jasoneplumb/infobento.com/previews/A-commuter.png

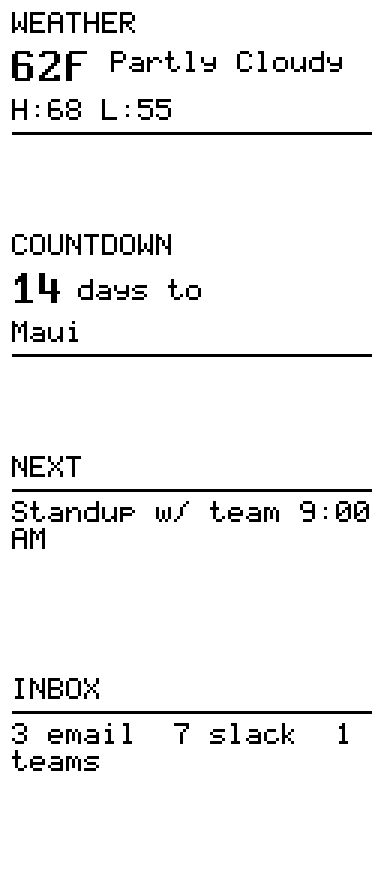
previews/A-commuter.png
