jasoneplumb/infobento.com/previews/C-networking-3color.png

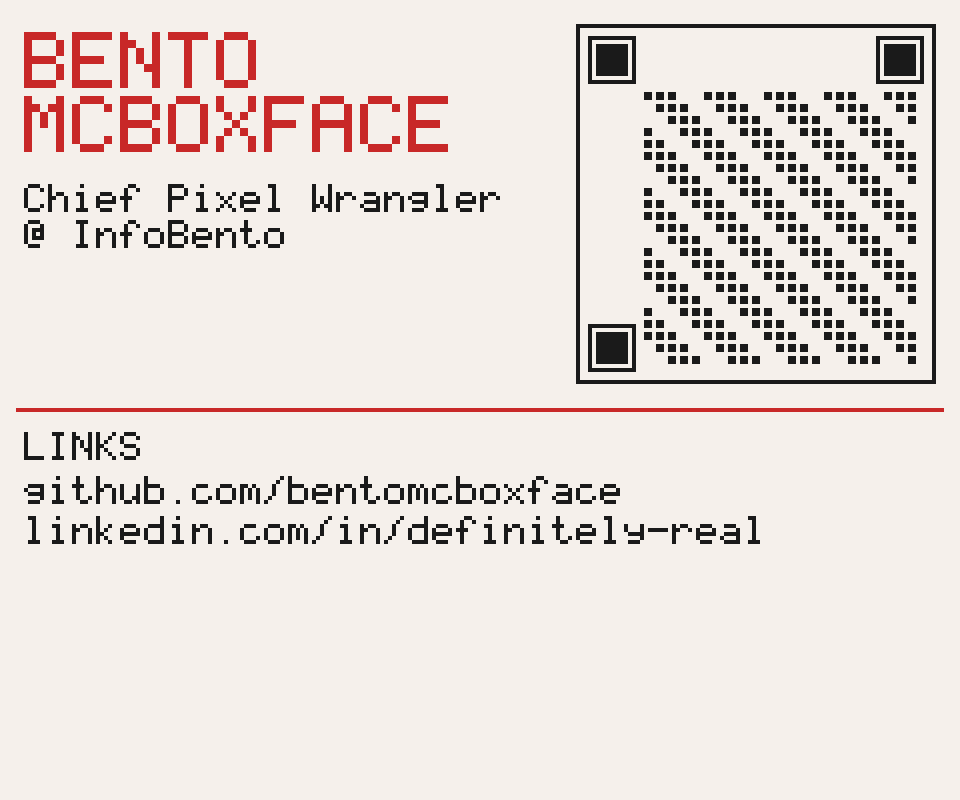
previews/C-networking-3color.png
