jasoneplumb/infobento.com/previews/C-networking.png

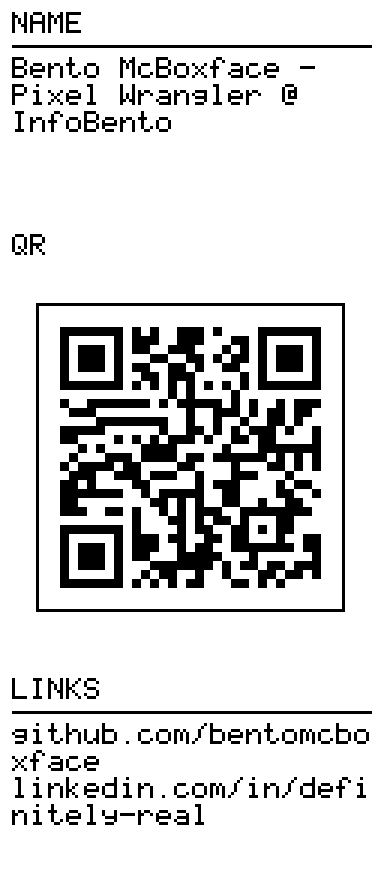
previews/C-networking.png
