jasoneplumb/infobento.com/previews/D-kitchen.png

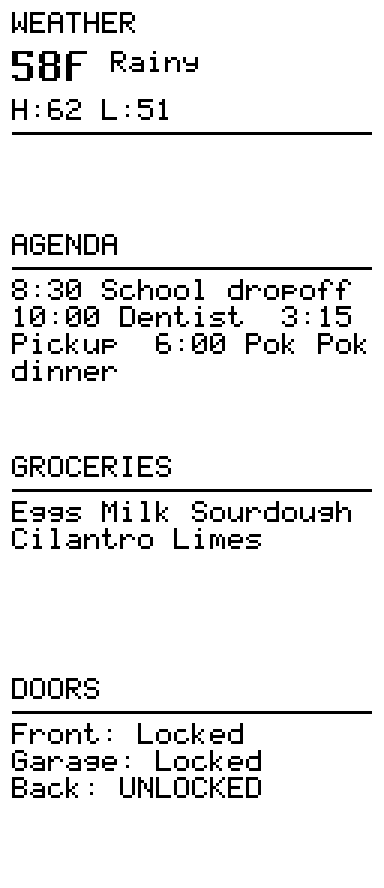
previews/D-kitchen.png
