jasoneplumb/infobento.com/previews/E-minimal.png

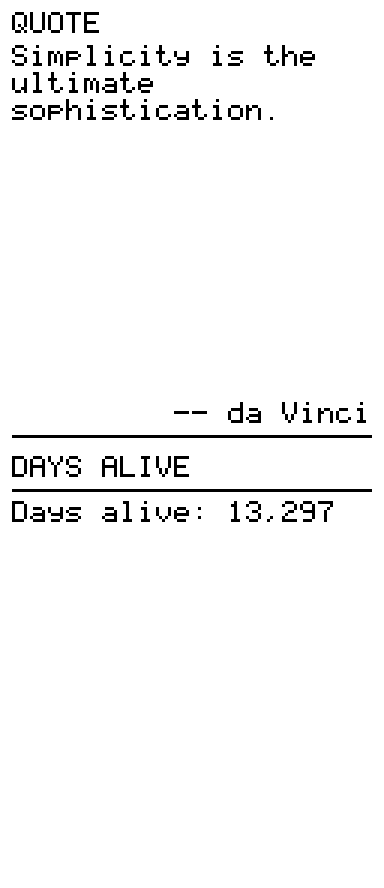
previews/E-minimal.png
