jasoneplumb/infobento.com/previews/F-busyparent.png

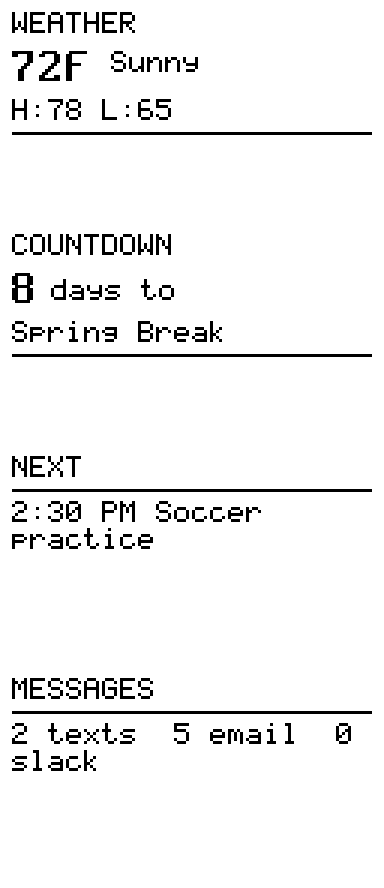
previews/F-busyparent.png
