jasoneplumb/infobento.com/previews/F-maxdensity.png

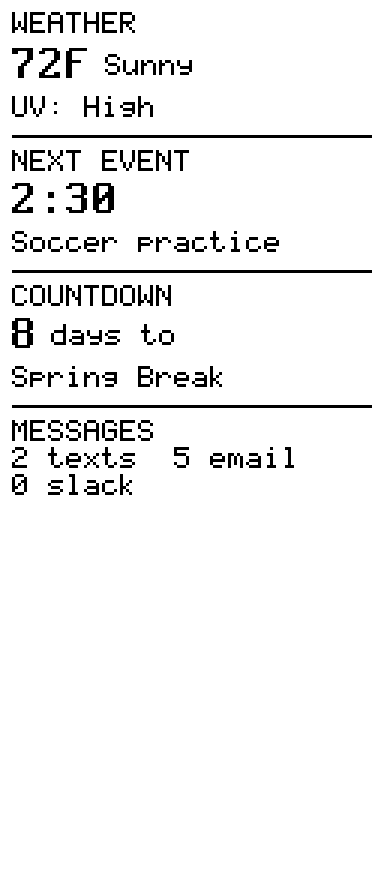
previews/F-maxdensity.png
