jasoneplumb/infobento.com/previews/F-spleen-8x16.png

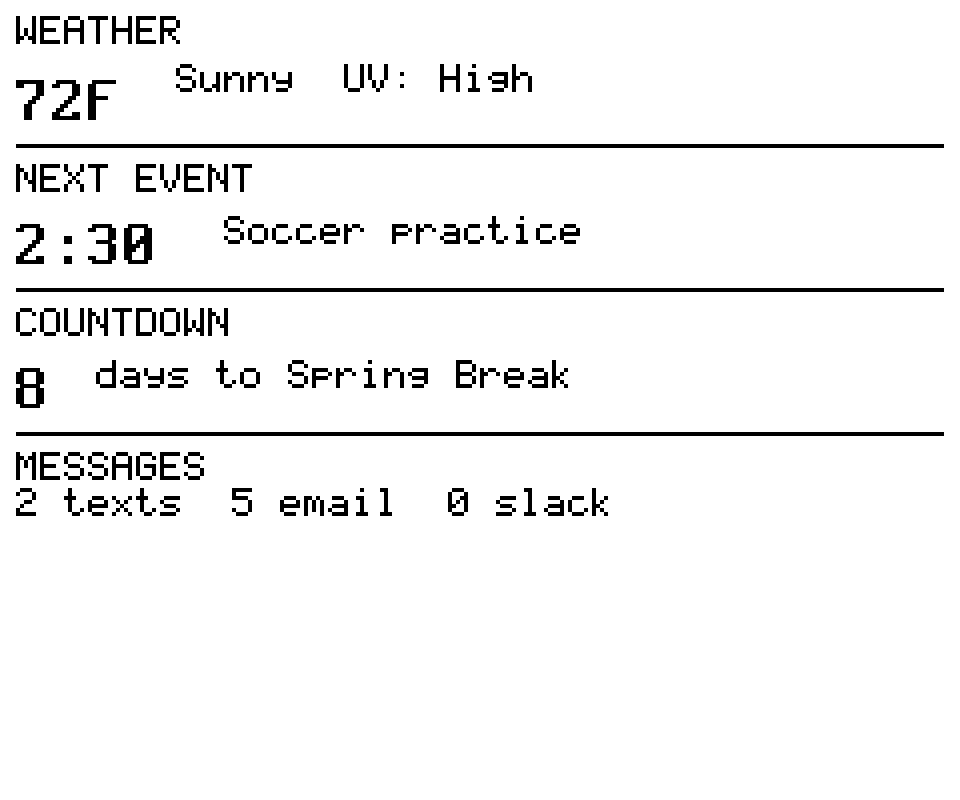
previews/F-spleen-8x16.png
