jasoneplumb/infobento.com/previews/F-tamzen-10x20.png

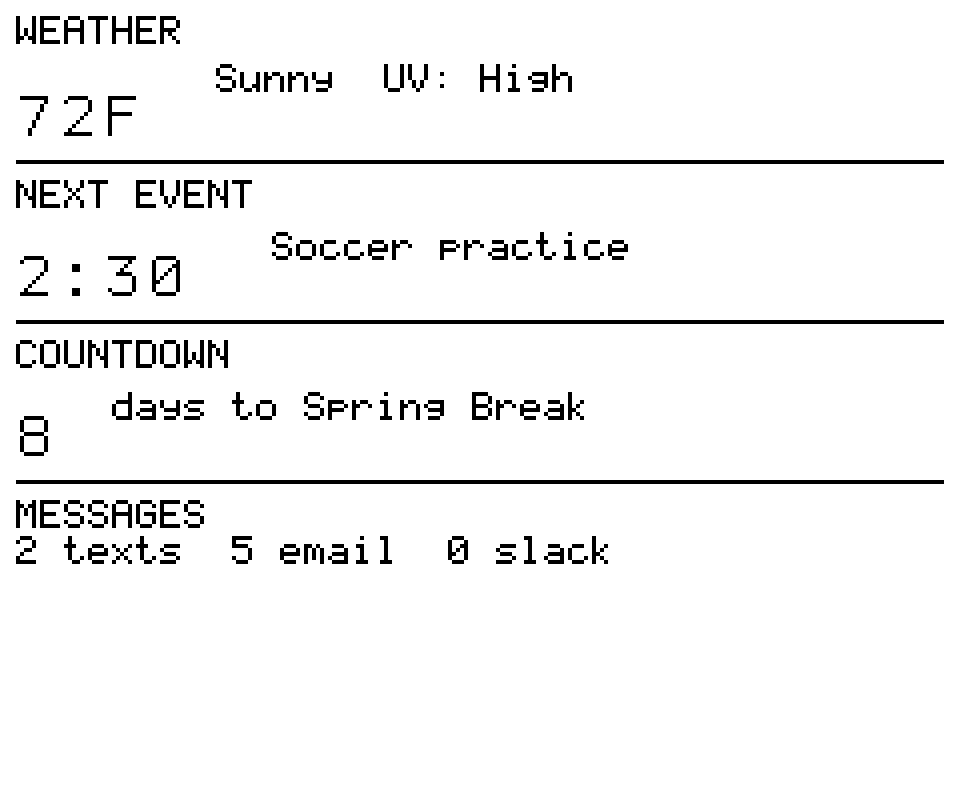
previews/F-tamzen-10x20.png
