jasoneplumb/infobento.com/previews/mode-closed.png

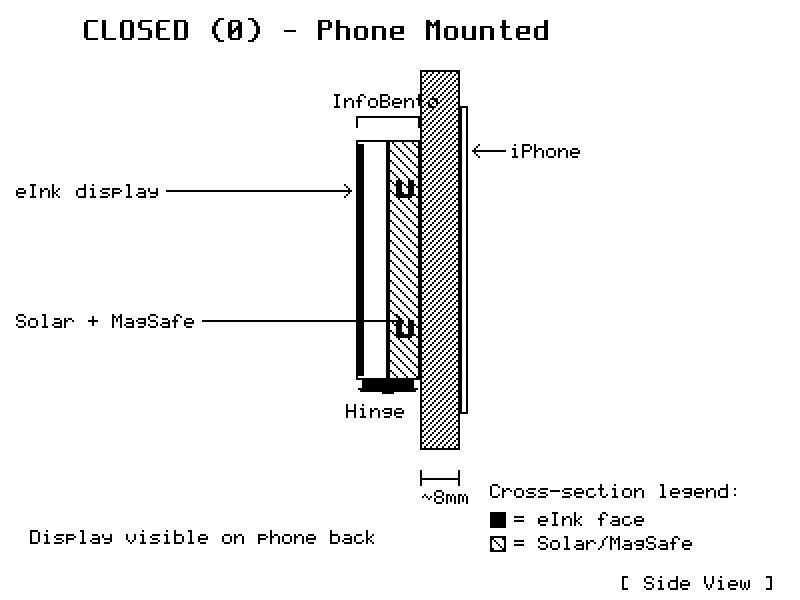
previews/mode-closed.png
