jasoneplumb/infobento.com/previews/mode-counter.png

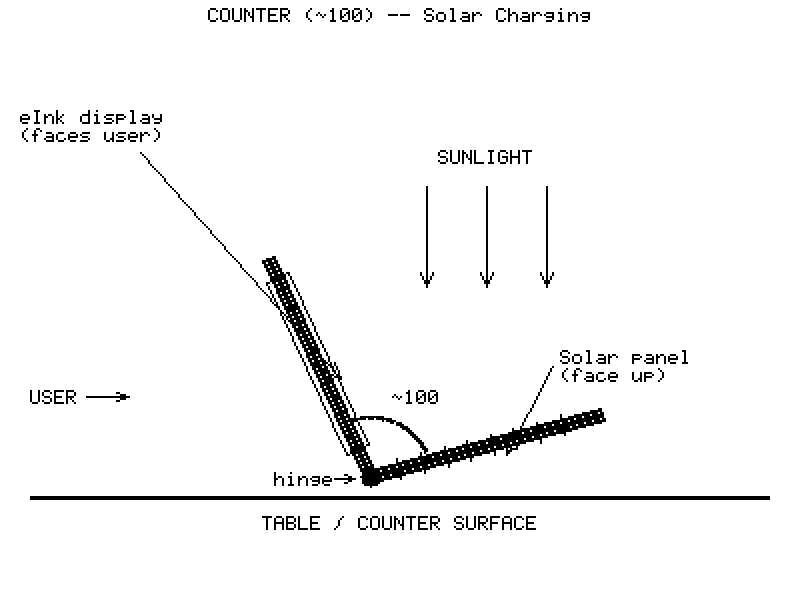
previews/mode-counter.png
