jasoneplumb/infobento.com/previews/mode-flat.png

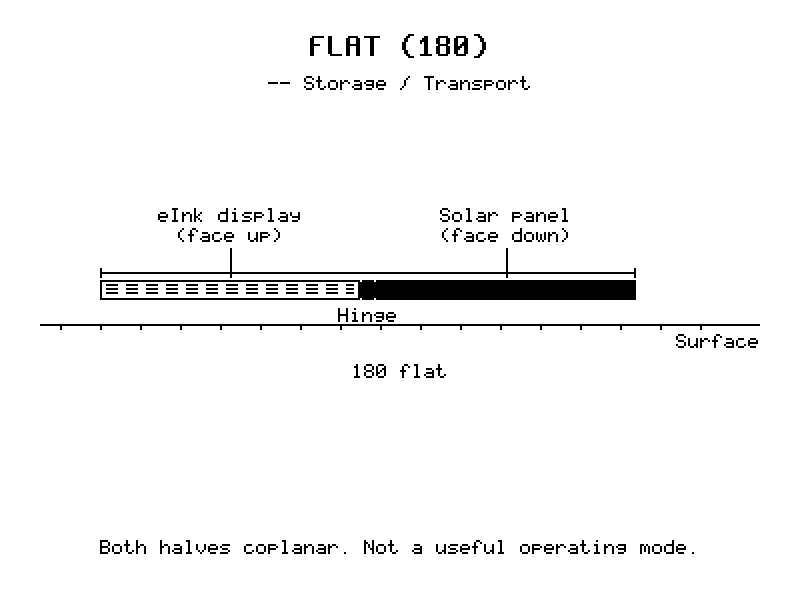
previews/mode-flat.png
