jasoneplumb/infobento.com/previews/mode-peek.png

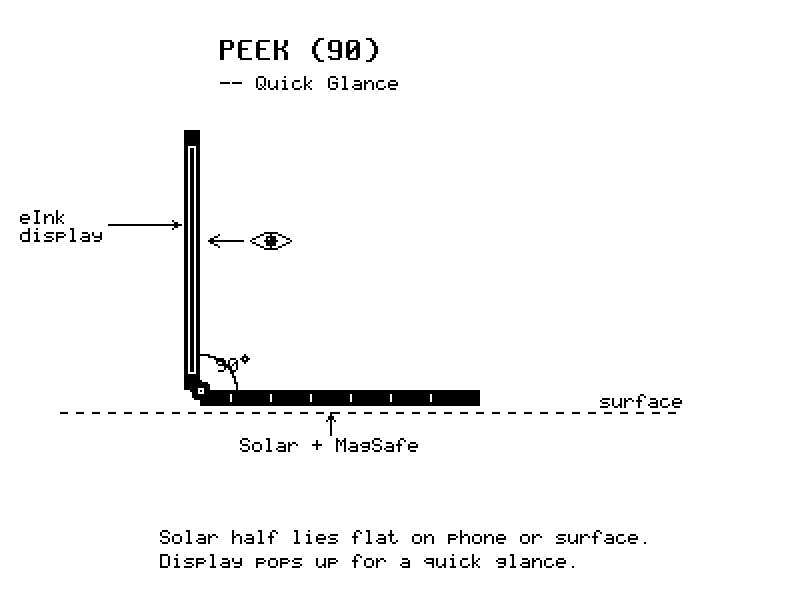
previews/mode-peek.png
