jasoneplumb/infobento.com/screenshots/unexpected-corner-appearance.png

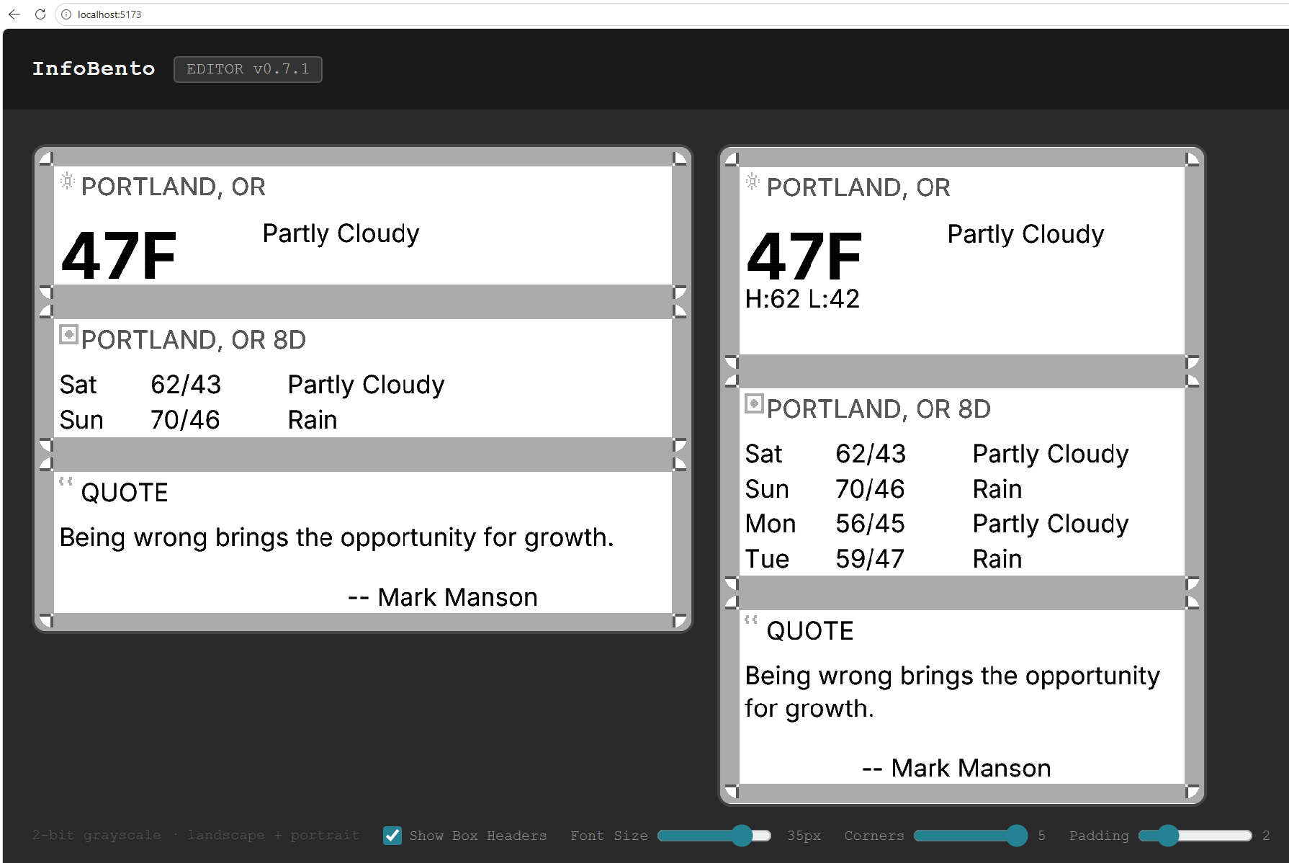
screenshots/unexpected-corner-appearance.png
