jasoneplumb/infobento.com/screenshots/unexpected-layout.png

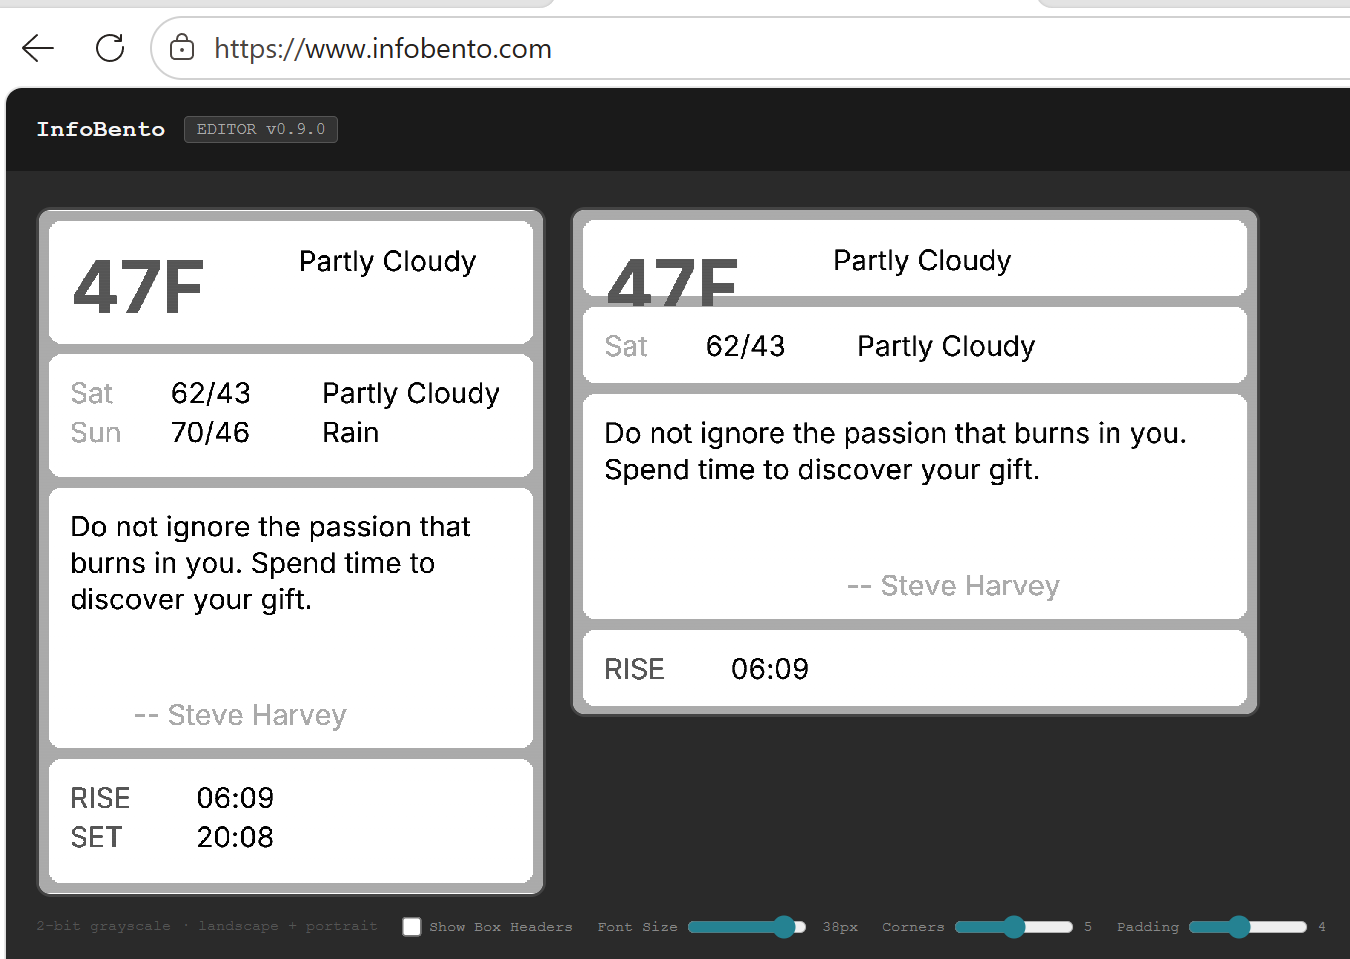
screenshots/unexpected-layout.png
