jasoneplumb/infobento.com/screenshots/unexpected-space-in-w-8d-layout.png

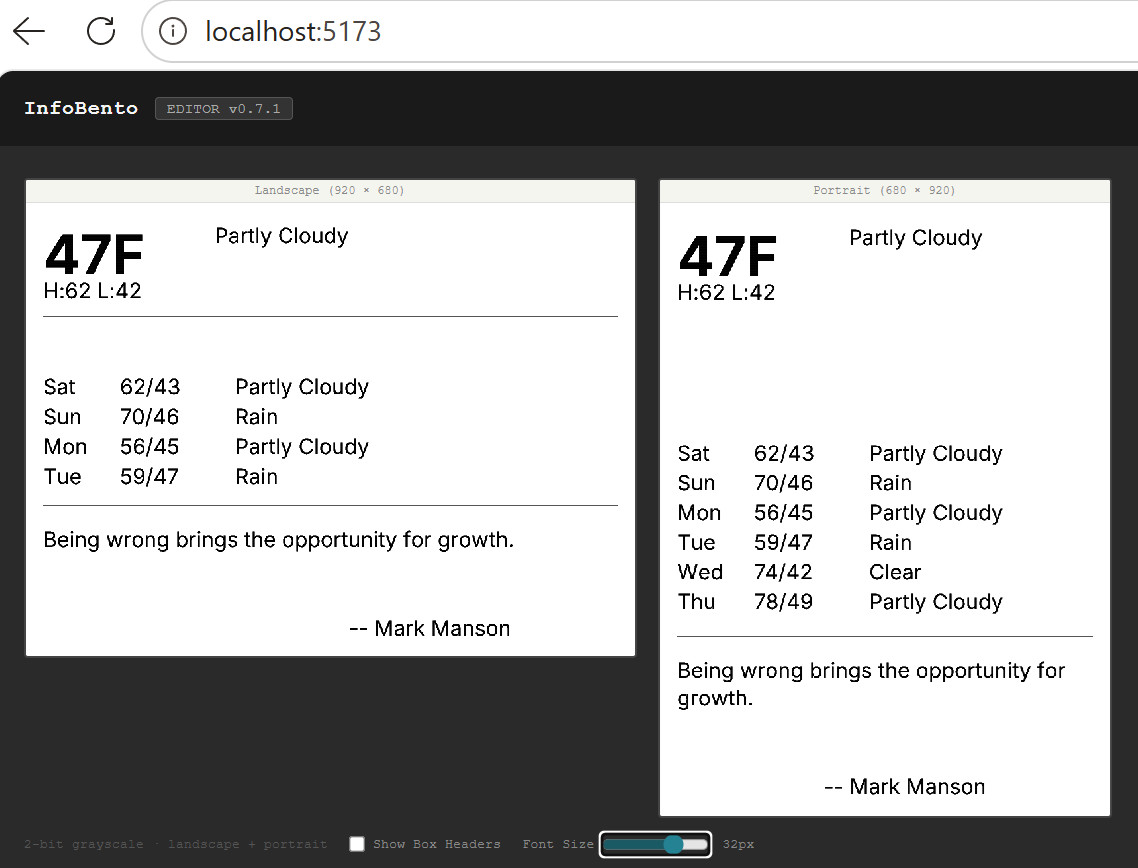
screenshots/unexpected-space-in-w-8d-layout.png
