jasoneplumb/infobento.com/.github/release-notes/v0.3.0.md

# v0.3.0 - Release Notes

### Added

- **PNG preview endpoint** — `POST /api/preview` renders bento configs as PNG images with optional `?scale=N` upscaling (#19)
- **MagSafe clamshell form factor** — 320-degree hinge connecting eInk display and solar panel. Three modes: phone-mounted (peek without unlocking), counter-standing (solar charges, display faces room), collapsed (MagSafe reverse-charge from iPhone)
- **Hardware platform** — ESP32-C3 (RISC-V, BLE 5.0), solar drip charger, MagSafe magnet ring. Must fit on iPhone 15 Pro back (146.6 x 70.6mm)
- **Value proposition** — "See less. Know enough." Anti-phone positioning: the screen that keeps you from reaching for one. $25 target via Kickstarter
- **Dual-mode power budget** — Counter-standing (1-2 refreshes/day, solar) and phone-mounted (minute-level partial refresh, MagSafe charging)
- **Phone-back peek scenario** — Primary daily use case: flip phone over, glance at eInk, move on without unlocking

### Changed

- **Project phase** advanced from `design` to `implement`
- **README** rewritten with tagline, form factor modes diagram, and hardware specs
- **Hardware docs** (display, power, BLE) updated for ESP32-C3, dual operating modes, and MagSafe
- **Architecture docs** updated with physical modes table and new system overview
- **"Zero Device Interaction"** design principle replaces "Zero Daily Interaction" — zero interaction with the InfoBento itself, not zero interaction period
- **API docs** — preview endpoint status updated from "planned" to implemented

### Known Issues

- Display resolution mismatch: codebase uses 240x200, standard 2.9" eInk panels are 296x128. Deferred until hardware finalized.

---

**Full Changelog**: https://github.com/jasoneplumb/infobento.com/compare/v0.2.0...v0.3.0
