jasoneplumb/infobento.com/.github/release-notes/v0.2.0.md

# v0.2.0 - Release Notes

### Added

- **Core types** — `TextBoxConfig`, `BoxConfig` discriminated union, `LayoutBox`, `LayoutResult` for typed bento box configurations
- **Layout engine** — `calculateLayout()` arranges boxes vertically in the 240x200 display with QR-aware height allocation (~50% for QR boxes) and 1px dividers
- **Embedded bitmap font** — 5x7 fixed-width font covering ASCII 32-126 (95 glyphs), embedded as pure data with zero external dependencies
- **Drawing primitives** — `setPixel`, `drawHLine/VLine`, `drawRect`, `drawChar`, `drawText`, `drawTextWrapped` with word wrapping
- **Text box renderer** — First box type: renders border, label header, dotted divider, and wrapped text content
- **Placeholder renderer** — Unsupported box types render as labeled bordered boxes until their renderer is implemented
- **28 tests** across 4 test files covering layout, drawing, font rendering, and end-to-end integration

### Changed

- **render()** now uses `calculateLayout()` and type-based dispatch instead of returning an empty frame buffer
- **Constants** extracted to `constants.ts` to avoid circular imports between layout and index modules

---

**Full Changelog**: https://github.com/jasoneplumb/infobento.com/compare/v0.1.0...v0.2.0
